DEAD10C5/bat_mini/eagle/bat_mini7.sch

## EAGLE design eagle/bat_mini7.sch (2018-07-10)

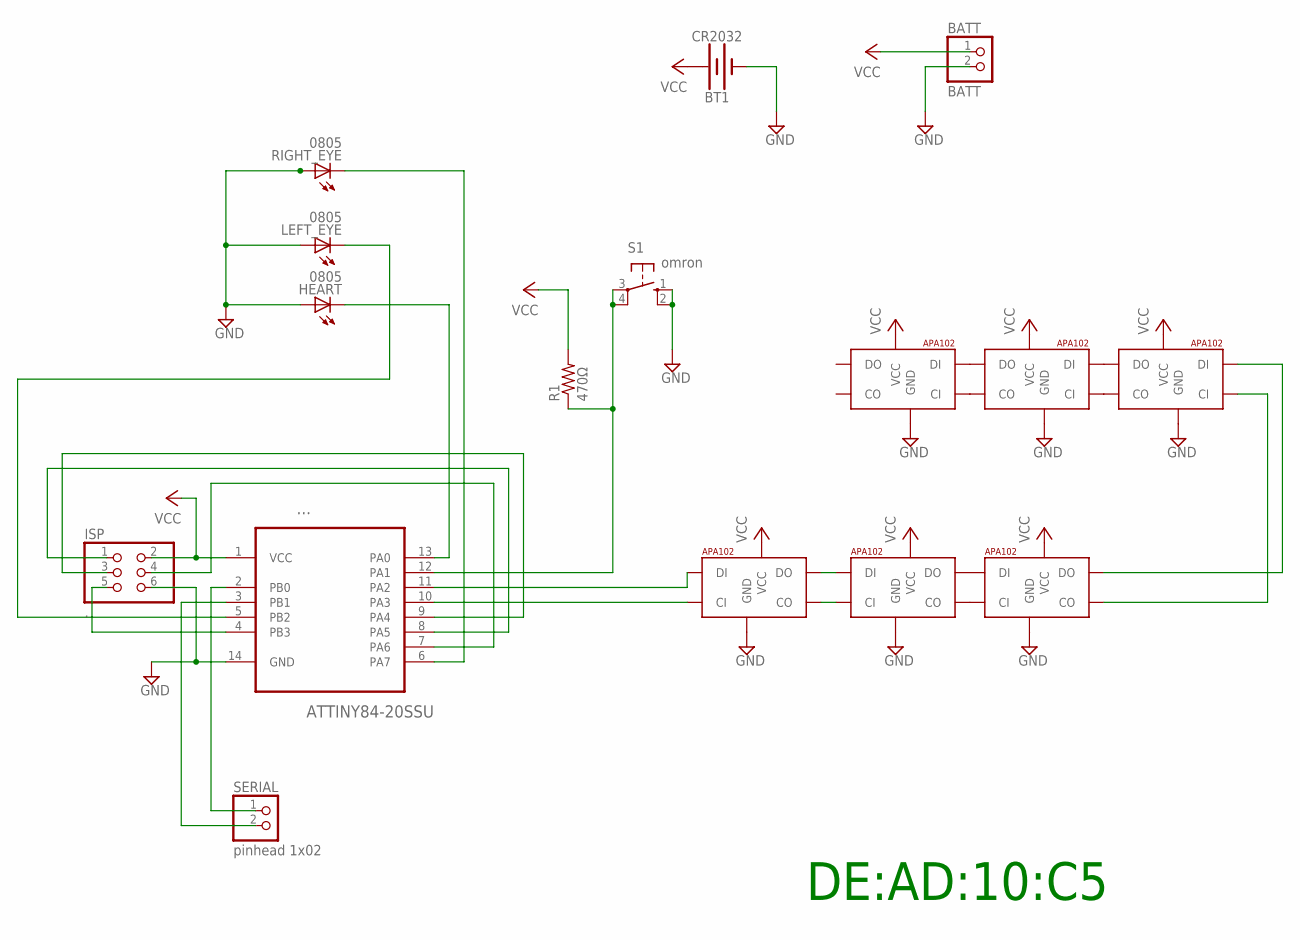
[picture p5: schematic bat_mini7.sch]

Parts:
...: ATTINY84-20SSU; SOIC127P600X175-14N
BATT: BATT; 1X02
BT1: CR2032; BATTCON_20MM_4LEGS
HEART: 0805; CHIP-LED0805
ISP: .; 2X03
LEFT_EYE: 0805; CHIP-LED0805
R1: 470Ω; R0805
RIGHT_EYE: 0805; CHIP-LED0805
S1: omron; B3F-10XX
SERIAL: pinhead 1x02; 1X02
U$1, U$2, U$3, U$5, U$6, U$7: APA1025050; APA102_5050

Connections:
GND: ....14 (GND), BATT.2, BT1.NEGATIVE (-), HEART.A, ISP.6, LEFT_EYE.A, RIGHT_EYE.A, S1.1 (S), S1.2 (S1), U$1.6 (GND), U$2.6 (GND), U$3.6 (GND), U$5.6 (GND), U$6.6 (GND), U$7.6 (GND)
unnamed: ....2 (PB0), SERIAL.1
unnamed: ....5 (PB2), LEFT_EYE.C
unnamed: ....8 (PA5), ISP.1
unnamed: ....7 (PA6), ISP.4
unnamed: ....9 (PA4), ISP.3
unnamed: ....4 (PB3), ISP.5
unnamed: ....13 (PA0), HEART.C
unnamed: ....6 (PA7), RIGHT_EYE.C
unnamed: ....11 (PA2), U$1.4 (DI)
unnamed: ....10 (PA3), U$1.5 (CI)
unnamed: U$2.3 (DO), U$3.4 (DI)
unnamed: ....12 (PA1), R1.1, S1.3, S1.4 (P1)
unnamed: U$1.3 (DO), U$2.4 (DI)
unnamed: U$1.2 (CO), U$2.5 (CI)
unnamed: ....3 (PB1), SERIAL.2
unnamed: U$2.2 (CO), U$3.5 (CI)
unnamed: U$5.3 (DO), U$6.4 (DI)
unnamed: U$5.2 (CO), U$6.5 (CI)
unnamed: U$6.3 (DO), U$7.4 (DI)
unnamed: U$6.2 (CO), U$7.5 (CI)
unnamed: U$3.3 (DO), U$5.4 (DI)
unnamed: U$3.2 (CO), U$5.5 (CI)
VCC: ....1 (VCC), BATT.1, BT1.POSITIVE@1 (+), ISP.2, R1.2, U$1.1 (VCC), U$2.1 (VCC), U$3.1 (VCC), U$5.1 (VCC), U$6.1 (VCC), U$7.1 (VCC)

Notes on the sheet:
DE:AD:10:C5
