DEAD10C5/bat_mini/eagle/bat_mini_drby_2018.sch

## EAGLE design eagle/bat_mini_drby_2018.sch (2018-09-06)

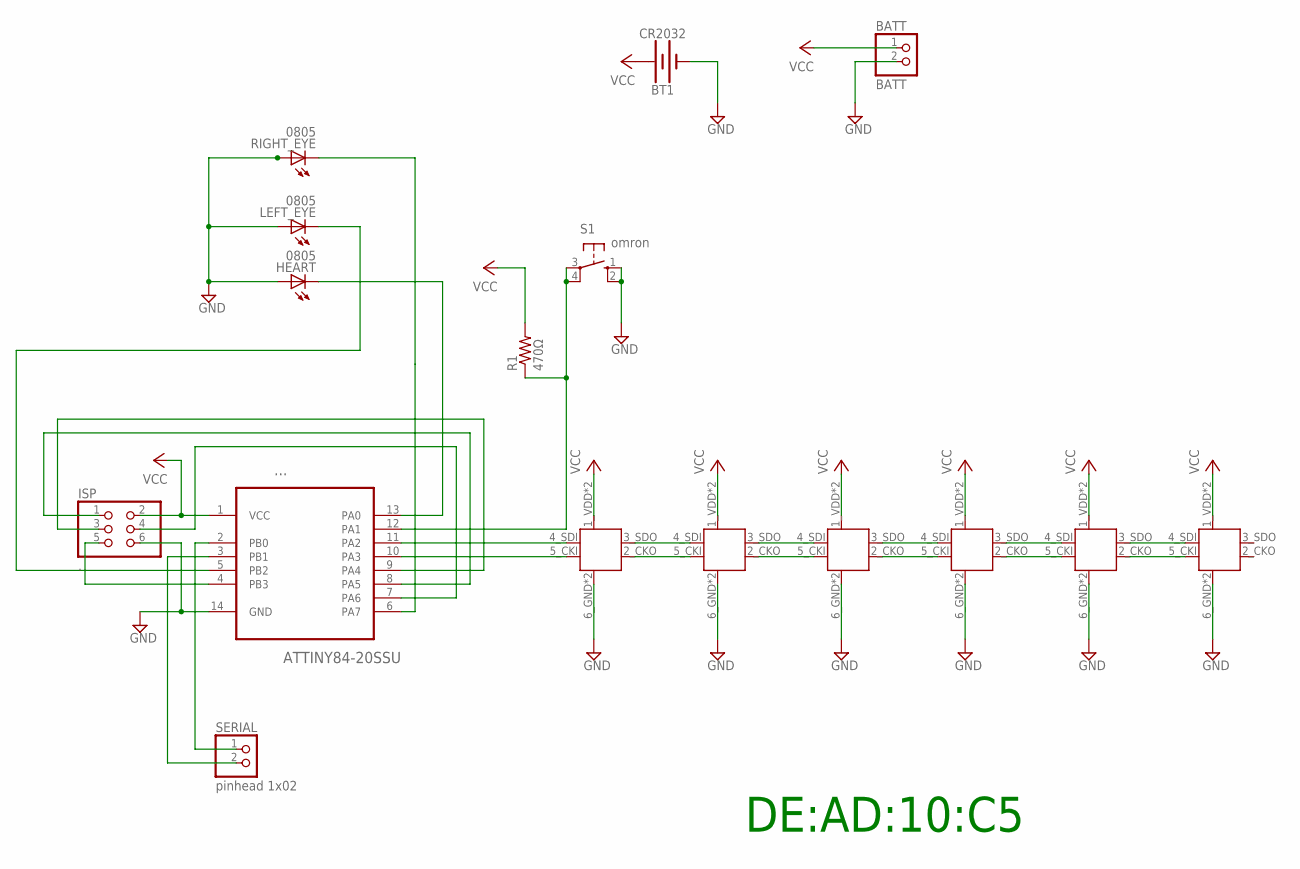
[picture p6: schematic bat_mini_drby_2018.sch]

Parts:
...: ATTINY84-20SSU; SOIC127P600X175-14N
BATT: BATT; 1X02
BT1: CR2032; BATTCON_20MM_4LEGS
HEART: 0805; CHIP-LED0805
ISP: .; 2X03
LEFT_EYE: 0805; CHIP-LED0805
R1: 470Ω; R0805
RIGHT_EYE: 0805; CHIP-LED0805
S1: omron; B3F-10XX
SERIAL: pinhead 1x02; 1X02
U$4, U$8, U$9, U$10, U$11, U$12: APA102; APA102-2020

Connections:
GND: ....14 (GND), BATT.2, BT1.NEGATIVE (-), HEART.A, ISP.6, LEFT_EYE.A, RIGHT_EYE.A, S1.1 (S), S1.2 (S1), U$4.6_GND (GND), U$8.6_GND (GND), U$9.6_GND (GND), U$10.6_GND (GND), U$11.6_GND (GND), U$12.6_GND (GND)
unnamed: ....2 (PB0), SERIAL.1
unnamed: ....5 (PB2), LEFT_EYE.C
unnamed: ....8 (PA5), ISP.1
unnamed: ....7 (PA6), ISP.4
unnamed: ....9 (PA4), ISP.3
unnamed: ....4 (PB3), ISP.5
unnamed: ....6 (PA7), RIGHT_EYE.C
unnamed: ....13 (PA0), HEART.C
unnamed: ....11 (PA2), U$4.4_SDI (SDI)
unnamed: ....10 (PA3), U$4.5_CKI (CKI)
unnamed: ....12 (PA1), R1.1, S1.3, S1.4 (P1)
unnamed: ....3 (PB1), SERIAL.2
unnamed: U$4.3_SDO (SDO), U$8.4_SDI (SDI)
unnamed: U$4.2_CKO (CKO), U$8.5_CKI (CKI)
unnamed: U$8.3_SDO (SDO), U$9.4_SDI (SDI)
unnamed: U$8.2_CKO (CKO), U$9.5_CKI (CKI)
unnamed: U$9.3_SDO (SDO), U$10.4_SDI (SDI)
unnamed: U$9.2_CKO (CKO), U$10.5_CKI (CKI)
unnamed: U$10.3_SDO (SDO), U$11.4_SDI (SDI)
unnamed: U$10.2_CKO (CKO), U$11.5_CKI (CKI)
unnamed: U$11.3_SDO (SDO), U$12.4_SDI (SDI)
unnamed: U$11.2_CKO (CKO), U$12.5_CKI (CKI)
VCC: ....1 (VCC), BATT.1, BT1.POSITIVE@1 (+), ISP.2, R1.2, U$4.1_VDD (VCC), U$8.1_VDD (VCC), U$9.1_VDD (VCC), U$10.1_VDD (VCC), U$11.1_VDD (VCC), U$12.1_VDD (VCC)

Notes on the sheet:
DE:AD:10:C5
