DEAD10C5/bat_mini/arduino/bat_mini_2018/bat_mini.cpp

/*!
 * @file bat_mini.cpp
    ____  _____      _    ____    _  ___     ____ ____
   |  _ \| ____|_   / \  |  _ \ _/ |/ _ \ _ / ___| ___|
   | | | |  _| (_) / _ \ | | | (_) | | | (_) |   |___ \
   | |_| | |___ _ / ___ \| |_| |_| | |_| |_| |___ ___) |
   |____/|_____(_)_/   \_\____/(_)_|\___/(_)\____|____/


   Author : @p0lr_ @mzbat @theDevilsVoice @dead10c5
   Date   : September 20th, 2018
   Version: 1.2
 * 
 * https://www.arduino.cc/en/Tutorial/ArduinoISP
 * Board: Attiny 24/44/84
 * Processor: ATtiny84
 * Clock: Internal 1MHz
 * Programmer: arduino as ISP
 */

#include "bat_mini.h"

/* Converts a color from HSV to RGB.
   h is hue, as a number between 0 and 360.
   s is the saturation, as a number between 0 and 255.
   v is the value, as a number between 0 and 255. */
rgb_color MyBat::hsvToRgb(uint16_t h, uint8_t s, uint8_t v)
{
  uint8_t f = (h % 60) * 255 / 60;
  uint8_t p = (255 - s) * (uint16_t)v / 255;
  uint8_t q = (255 - f * (uint16_t)s / 255) * (uint16_t)v / 255;
  uint8_t t = (255 - (255 - f) * (uint16_t)s / 255) * (uint16_t)v / 255;
  uint8_t r = 0, g = 0, b = 0;
  switch ((h / 60) % 6) {
    case 0: r = v; g = t; b = p; break;
    case 1: r = q; g = v; b = p; break;
    case 2: r = p; g = v; b = t; break;
    case 3: r = p; g = q; b = v; break;
    case 4: r = t; g = p; b = v; break;
    case 5: r = v; g = p; b = q; break;
  }
  return rgb_color(r, g, b);
}
